mistic100/xiao-round-screen-thermometer/firmware/data/bg.png

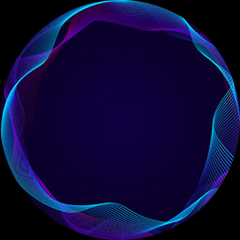
firmware/data/bg.png
