mistic100/xiao-round-screen-thermometer/firmware/src/secrets.tpl.h

#pragma once

#include <Arduino.h>

const String WIFI_SSID = "XXXX";
const String WIFI_PASS = "XXXX";
const String OTA_PASS = "XXXX";

const String HA_TOKEN = "Bearer XXXX";
const String HA_URL = "http://<your-ha-host>/api/states/";
const String HA_SENSOR = "<your-sensor-id>";
